ethomas997/RotorHazard-Race-Counter/firmware/RaceCounter/Orbitron50pt7b.h

const uint8_t Orbitron50pt7bBitmaps[] PROGMEM = {
  0x00, 0xFF, 0xFF, 0xFF, 0xFF, 0xFF, 0xFF, 0xFF, 0xFF, 0xFF, 0xFF, 0xFF,
  0xFF, 0xFF, 0xFF, 0xFF, 0xFF, 0xFF, 0xFF, 0xFF, 0xFF, 0xFF, 0xFF, 0xFF,
  0xFF, 0xFF, 0xFF, 0xFF, 0xFF, 0xFF, 0xFF, 0xFF, 0xFF, 0xFF, 0xFF, 0xFF,
  0xFF, 0xFF, 0xFF, 0xFF, 0xFF, 0xFF, 0xFF, 0xFF, 0xFF, 0xFF, 0xFF, 0xFF,
  0xFF, 0xFF, 0xFF, 0xFF, 0xFF, 0xFF, 0xFF, 0xFF, 0xFF, 0xFF, 0xFF, 0xFF,
  0xFF, 0xFF, 0xFF, 0xFF, 0xFF, 0xFF, 0xFF, 0xFF, 0xFF, 0xFF, 0xFF, 0xFF,
  0xFF, 0xFF, 0xFF, 0xFF, 0xFF, 0xFF, 0xFF, 0xFF, 0xFF, 0xFF, 0xFF, 0xFE,
  0x00, 0x00, 0x00, 0x00, 0x00, 0x00, 0x00, 0x00, 0x00, 0x07, 0xFF, 0xFF,
  0xFF, 0xFF, 0xFF, 0xFF, 0xFF, 0xFF, 0xFF, 0xFF, 0xFF, 0xFF, 0xFF, 0xFF,
  0xFF, 0xFF, 0xFF, 0xFF, 0xFF, 0xFF, 0xFC, 0xFF, 0xF9, 0xFF, 0xFF, 0xFF,
  0x9F, 0xFF, 0xFF, 0xF9, 0xFF, 0xFF, 0xFF, 0x9F, 0xFF, 0xFF, 0xF9, 0xFF,
  0xFF, 0xFF, 0x9F, 0xFF, 0xFF, 0xF9, 0xFF, 0xFF, 0xFF, 0x9F, 0xFF, 0xFF,
  0xF9, 0xFF, 0xFF, 0xFF, 0x9F, 0xFF, 0xFF, 0xF9, 0xFF, 0xFF, 0xFF, 0x9F,
  0xFF, 0xFF, 0xF9, 0xFF, 0xFF, 0xFF, 0x9F, 0xFF, 0xFF, 0xF9, 0xFF, 0xFF,
  0xFF, 0x9F, 0xFF, 0xFF, 0xF9, 0xFF, 0xFF, 0xFF, 0x9F, 0xFF, 0x00, 0x00,
  0x00, 0x3F, 0xFE, 0x00, 0x00, 0xFF, 0xF8, 0x00, 0x00, 0x00, 0xFF, 0xF8,
  0x00, 0x03, 0xFF, 0xE0, 0x00, 0x00, 0x01, 0xFF, 0xF0, 0x00, 0x07, 0xFF,
  0xC0, 0x00, 0x00, 0x03, 0xFF, 0xE0, 0x00, 0x0F, 0xFF, 0x80, 0x00, 0x00,
  0x0F, 0xFF, 0x80, 0x00, 0x3F, 0xFE, 0x00, 0x00, 0x00, 0x1F, 0xFF, 0x00,
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
  { 15256,  64,  70,  71,    6,  -69 },   // 0x46 'F'
  { 15816,  71,  70,  81,    5,  -69 },   // 0x47 'G'
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

const GFXfont Orbitron50pt7b PROGMEM = {
  (uint8_t  *)Orbitron50pt7bBitmaps,
  (GFXglyph *)Orbitron50pt7bGlyphs,
  0x20, 0x7E, 98 };

// Approx. 42503 bytes
